marceloschmitt1/ProjetoCisternasNasEscolasIoT/FotosCisternas-2018-04-20/20180206_130338.jpg

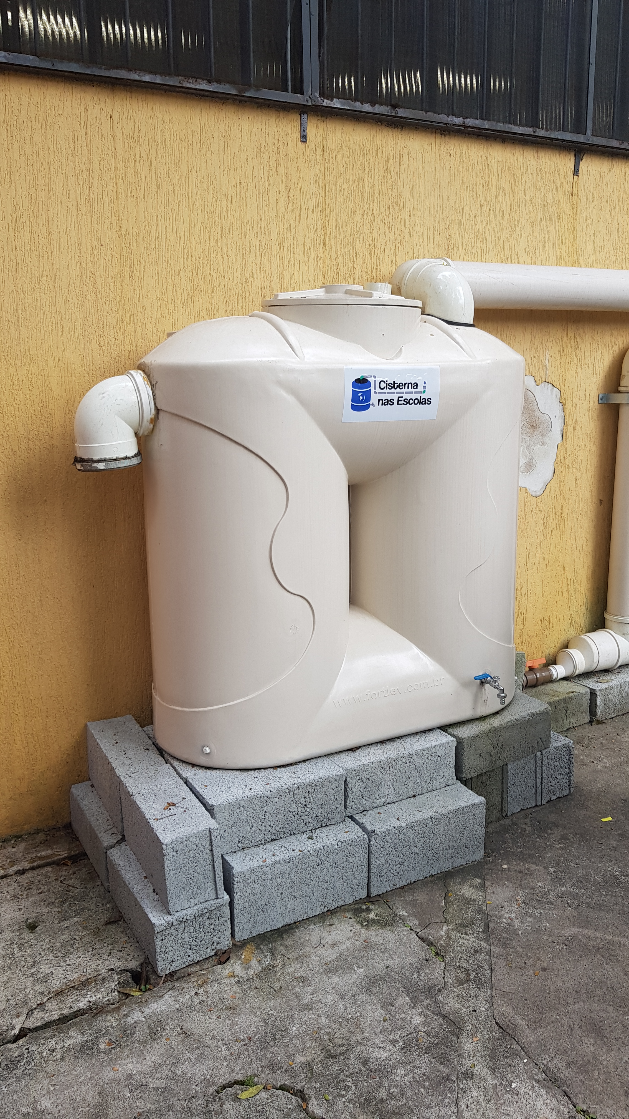
FotosCisternas-2018-04-20/20180206_130338.jpg
