marceloschmitt1/ProjetoCisternasNasEscolasIoT/SensorCapacitivoDeNivelDeFluido/20180510_110452.jpg

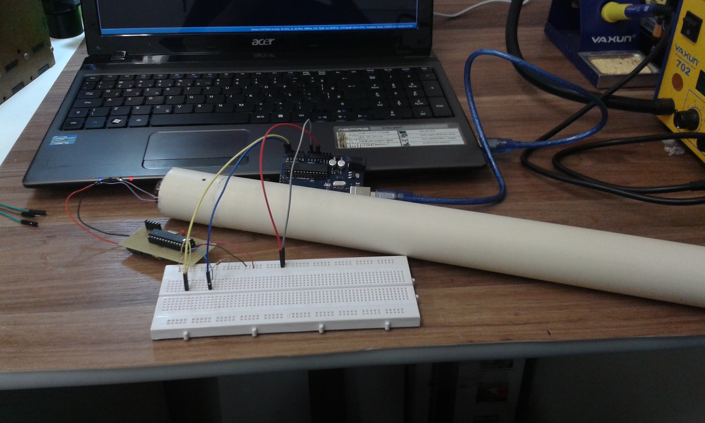
SensorCapacitivoDeNivelDeFluido/20180510_110452.jpg
