marceloschmitt1/ProjetoCisternasNasEscolasIoT/SensorCapacitivoDeNivelDeFluido/20180510_110459.jpg

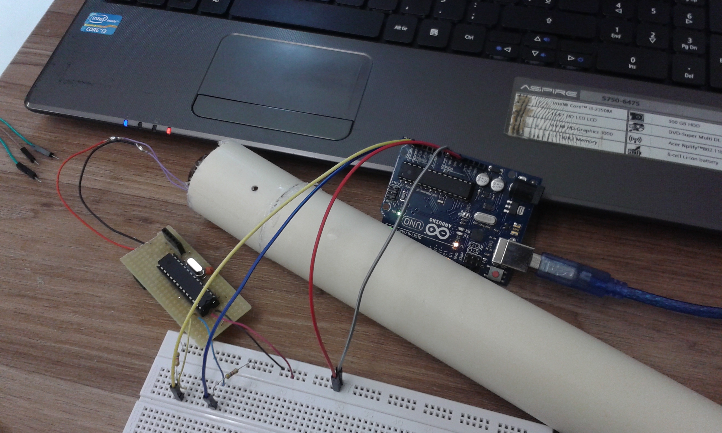
SensorCapacitivoDeNivelDeFluido/20180510_110459.jpg
