marceloschmitt1/ProjetoCisternasNasEscolasIoT/SensorDeForca/plano_detalhado.jpg

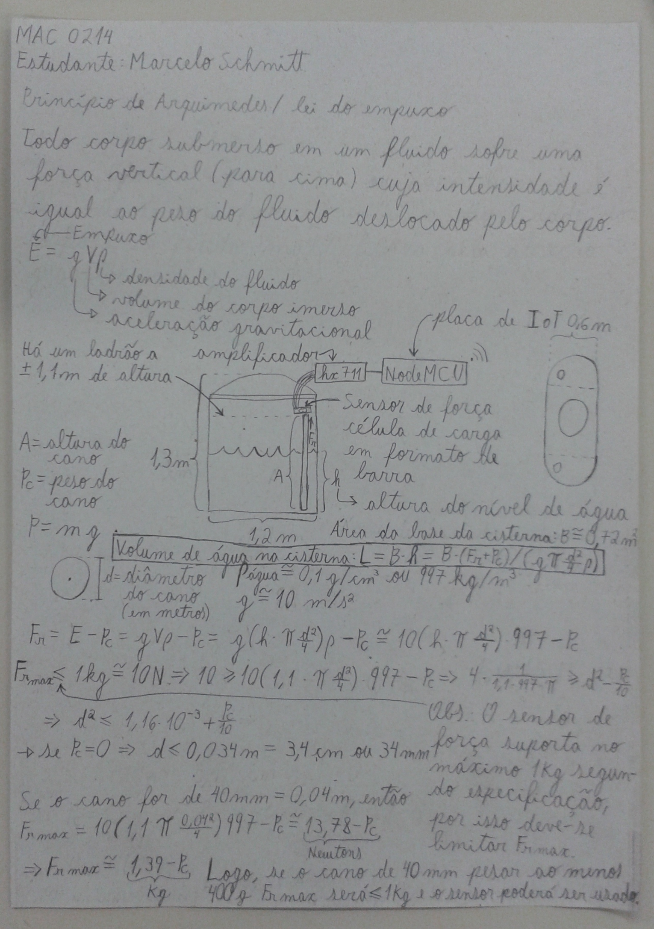
SensorDeForca/plano_detalhado.jpg
