marceloschmitt1/ProjetoCisternasNasEscolasIoT/SensorDeForca/sistema_medicao_base.jpg

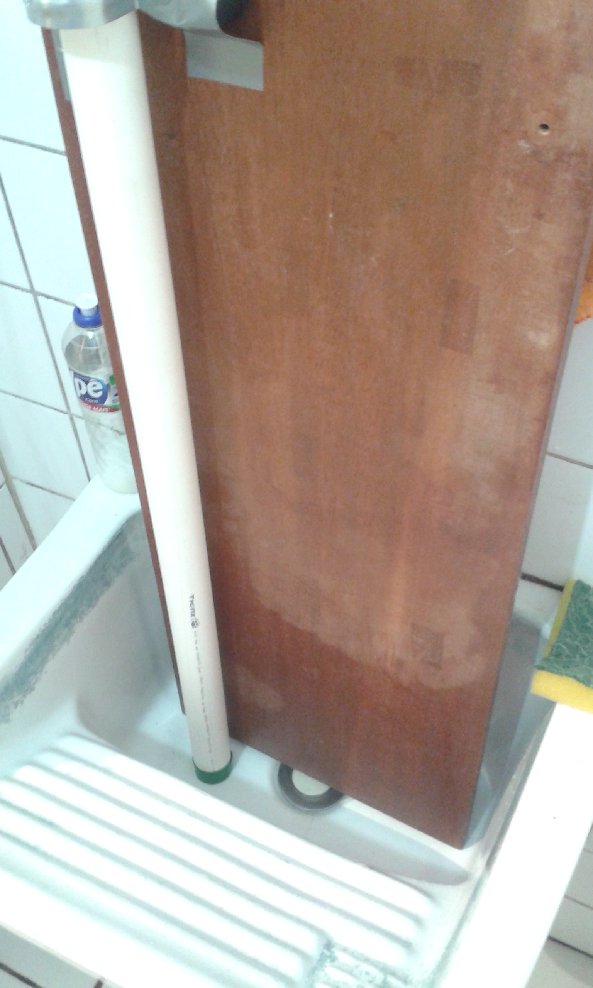
SensorDeForca/sistema_medicao_base.jpg
