marceloschmitt1/ProjetoCisternasNasEscolasIoT/SensorDeForca/sistema_medicao_circuitaria.jpg

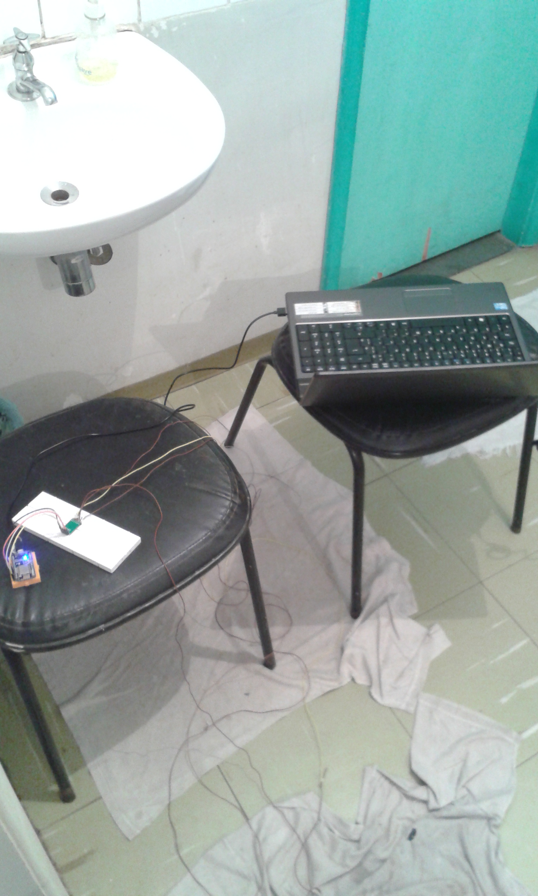
SensorDeForca/sistema_medicao_circuitaria.jpg
