marceloschmitt1/ProjetoCisternasNasEscolasIoT/SensorDeForca/sistema_medicao_frente.jpg

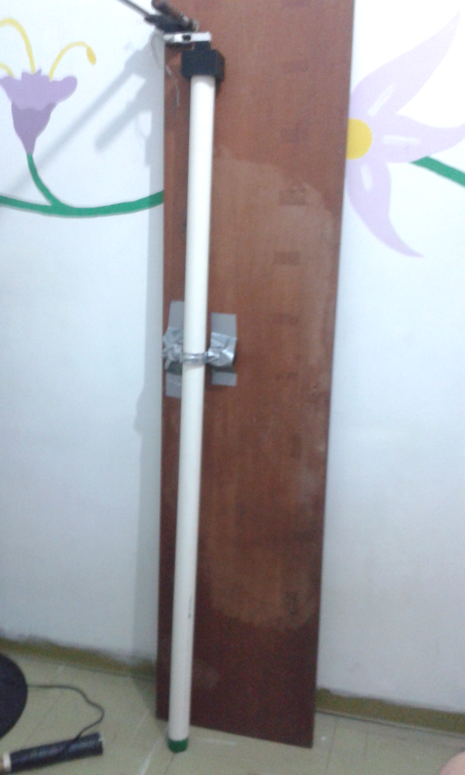
SensorDeForca/sistema_medicao_frente.jpg
