marceloschmitt1/ProjetoCisternasNasEscolasIoT/SensorDeForca/sistema_medicao_lado.jpg

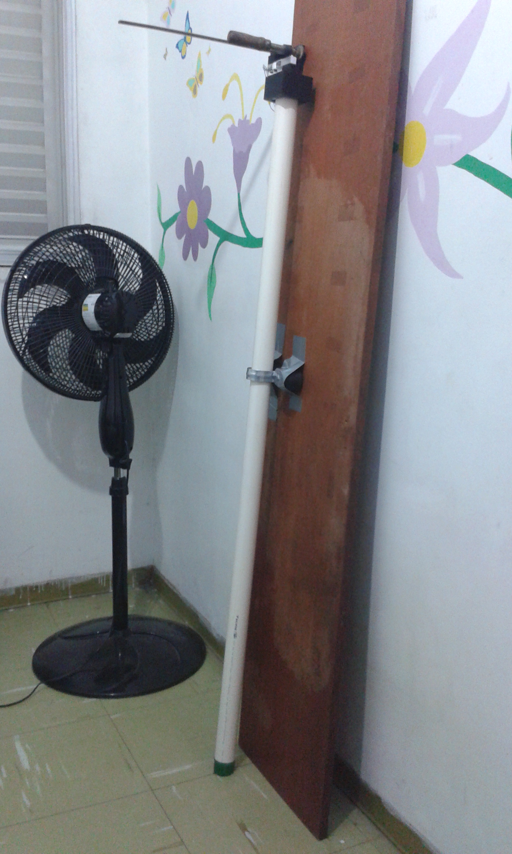
SensorDeForca/sistema_medicao_lado.jpg
