marceloschmitt1/ProjetoCisternasNasEscolasIoT/SensorDeForca/sistema_medicao_sensor.jpg

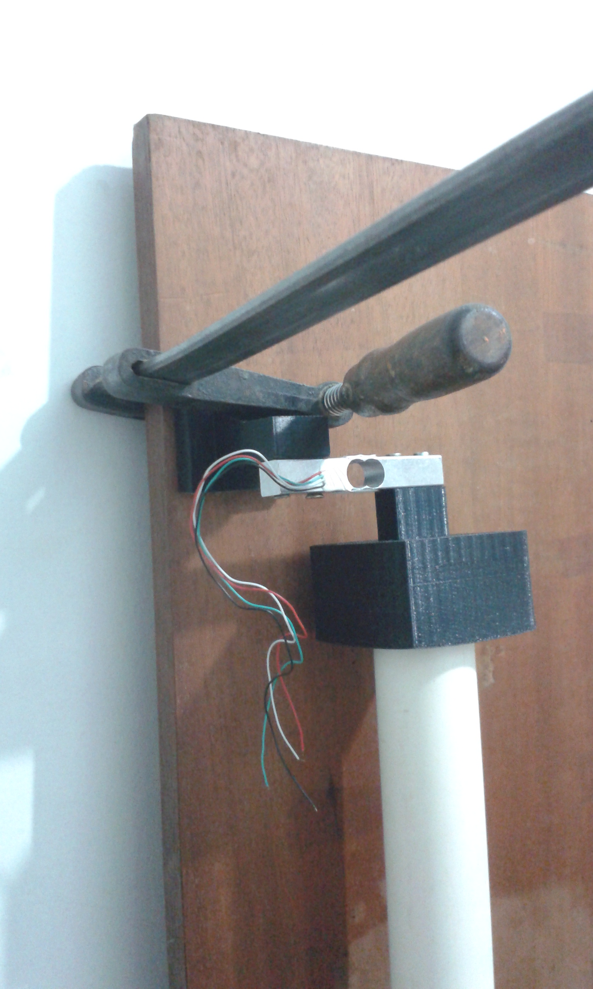
SensorDeForca/sistema_medicao_sensor.jpg
