marceloschmitt1/ProjetoCisternasNasEscolasIoT/site_cisternas/cisternas/Esboço tutorial.jpg

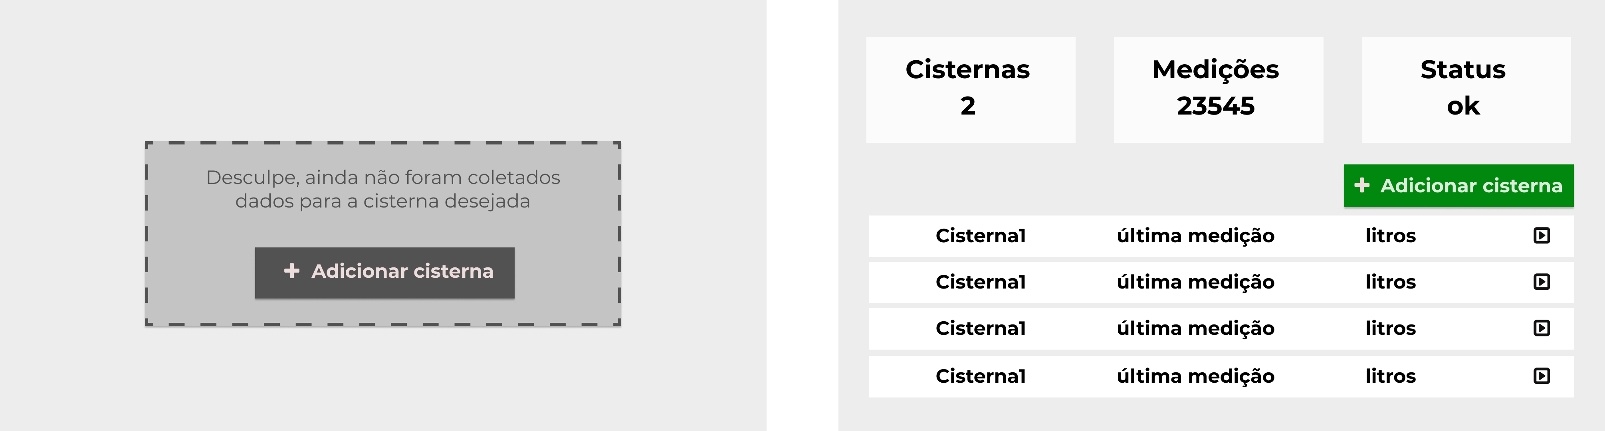
site_cisternas/cisternas/Esboço tutorial.jpg
