marceloschmitt1/ProjetoCisternasNasEscolasIoT/site_cisternas/site_cisternas/urls.py

"""site_cisternas URL Configuration

The `urlpatterns` list routes URLs to views. For more information please see:
    https://docs.djangoproject.com/en/2.0/topics/http/urls/
Examples:
Function views
    1. Add an import:  from my_app import views
    2. Add a URL to urlpatterns:  path('', views.home, name='home')
Class-based views
    1. Add an import:  from other_app.views import Home
    2. Add a URL to urlpatterns:  path('', Home.as_view(), name='home')
Including another URLconf
    1. Import the include() function: from django.urls import include, path
    2. Add a URL to urlpatterns:  path('blog/', include('blog.urls'))
"""
from django.contrib import admin
from django.urls import include, path


# from .router import router
# from . import router

from rest_framework import serializers, viewsets, routers
from cisternas.api.viewsets import CisternaViewSet, MedicaoViewSet

router = routers.DefaultRouter()
router.register('cisternas', CisternaViewSet)
router.register('medicoes', MedicaoViewSet)

# from . import views

app_name = 'cisternas'
urlpatterns = [
	# path('', views.index2, name='index2', kwargs={"arg0": 2}),
	# path('', views.index, name='index'),
	path('', include('cisternas.urls')),
	path('polls/', include('polls.urls')),
    path('admin/', admin.site.urls),
    path('api/', include(router.urls)),
]
# para incluir login e logout
urlpatterns += [
    path('api-auth/', include('rest_framework.urls')),
]
