marceloschmitt1/ProjetoCisternasNasEscolasIoT/site_cisternas/site_cisternas/wsgi.py

"""
WSGI config for site_cisternas project.

It exposes the WSGI callable as a module-level variable named ``application``.

For more information on this file, see
https://docs.djangoproject.com/en/2.0/howto/deployment/wsgi/
"""

import os

from django.core.wsgi import get_wsgi_application

os.environ.setdefault("DJANGO_SETTINGS_MODULE", "site_cisternas.settings")

application = get_wsgi_application()
